MontoIng/AvRC-MA/Diseño (muestras)/Avión desvaliajo'.jpeg

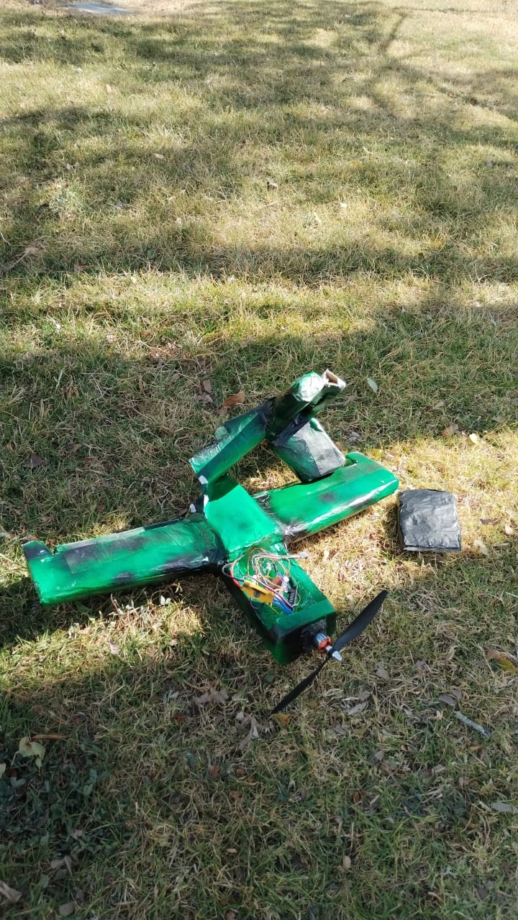
Diseño (muestras)/Avión desvaliajo'.jpeg
