MontoIng/AvRC-MA/Diseño (muestras)/Diseño avión.jpeg

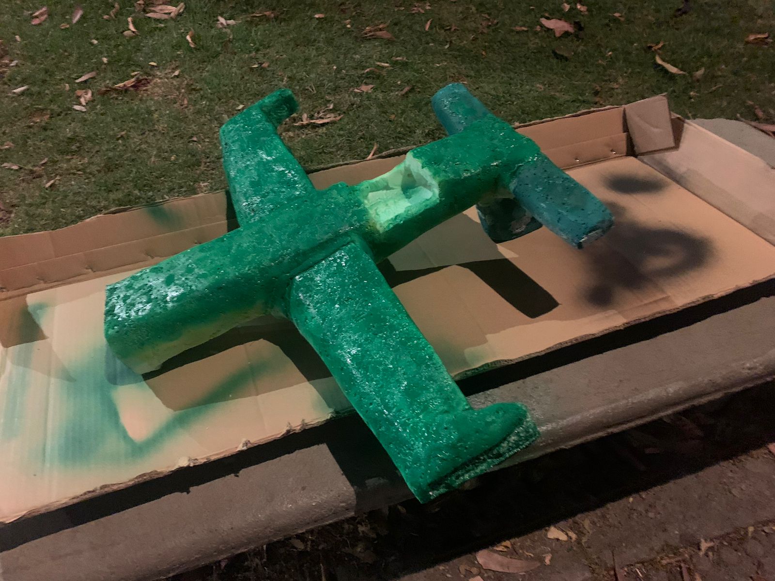
Diseño (muestras)/Diseño avión.jpeg
