MontoIng/AvRC-MA/Diseño (muestras)/Foto Avión - Control (en PROFI).jpeg

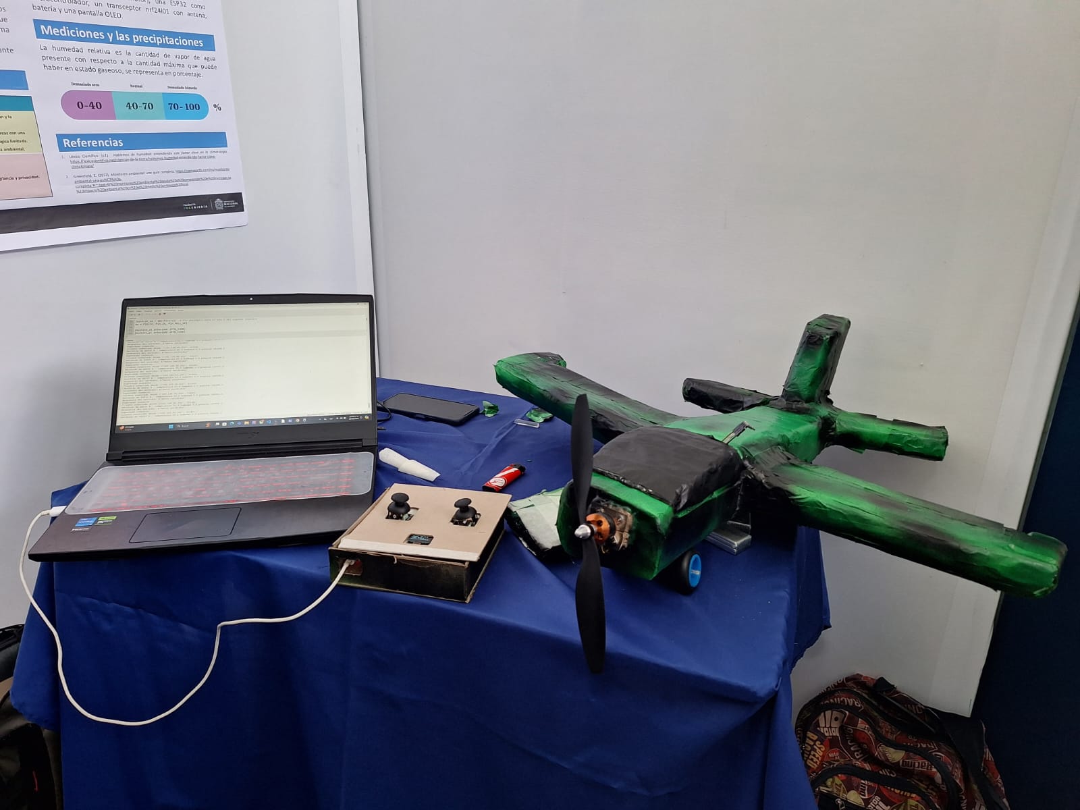
Diseño (muestras)/Foto Avión - Control (en PROFI).jpeg
