MontoIng/AvRC-MA/Documentos/Diagrama de Caja Negra.png

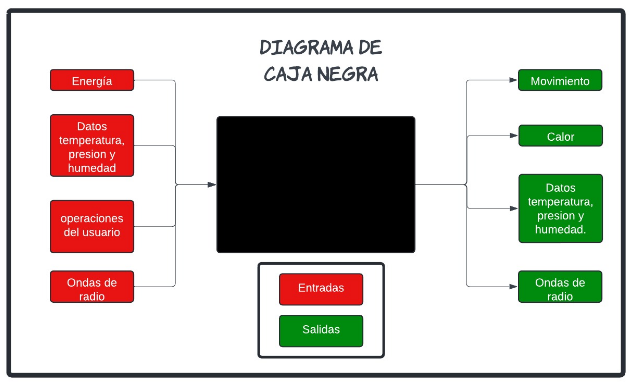
Documentos/Diagrama de Caja Negra.png
