MontoIng/AvRC-MA/Documentos/Diagrama Tecnológico.jpeg

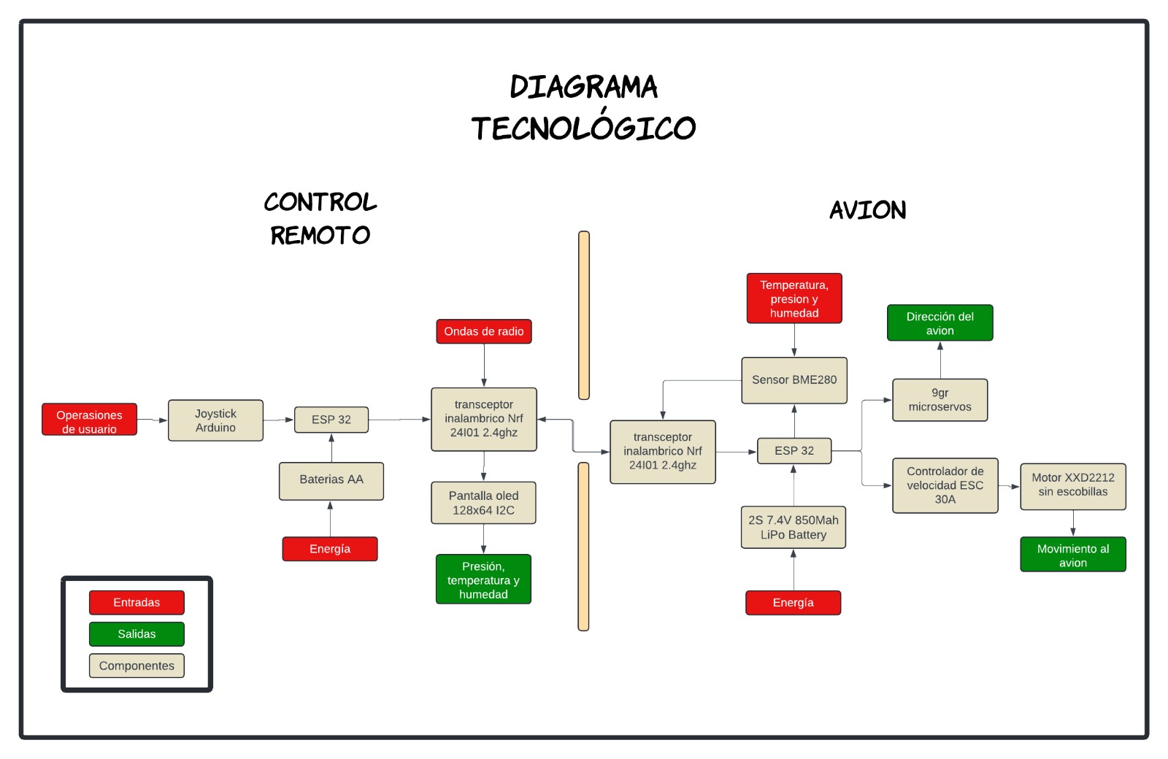
Documentos/Diagrama Tecnológico.jpeg
