MontoIng/AvRC-MA/Documentos/Función pantalla OLED (diagrama).jpeg

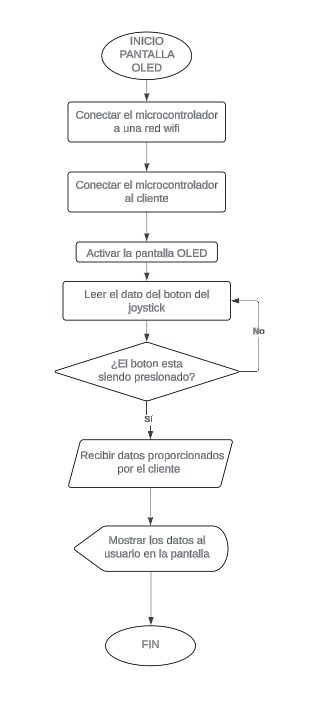
Documentos/Función pantalla OLED (diagrama).jpeg
