MontoIng/AvRC-MA/Documentos/Función sensor (diagrama).jpeg

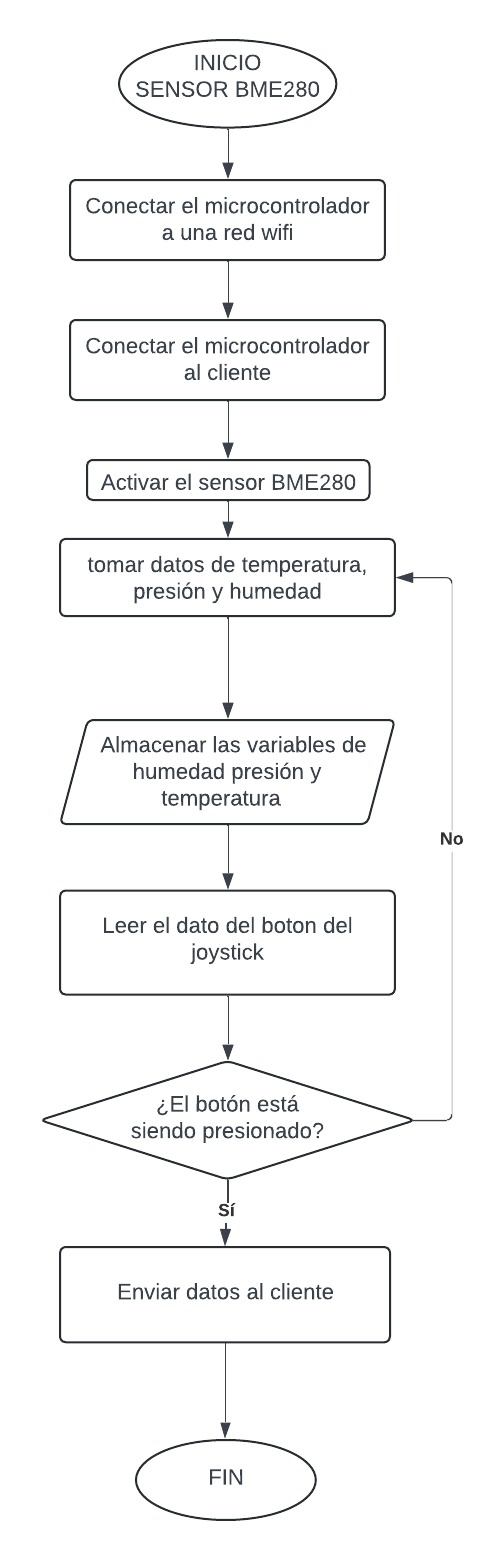
Documentos/Función sensor (diagrama).jpeg
