MontoIng/AvRC-MA/Documentos/Interacción desde motor (diagrama).jpeg

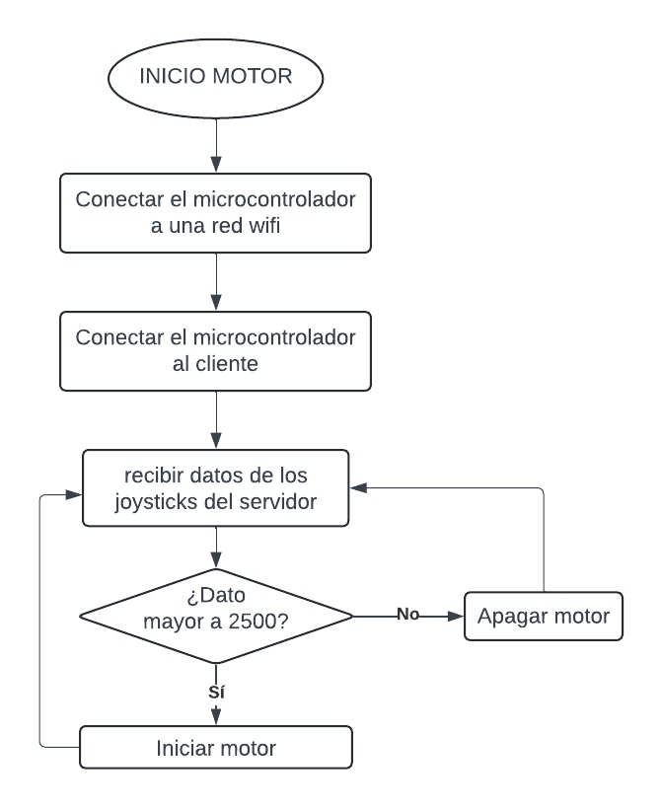
Documentos/Interacción desde motor (diagrama).jpeg
