MontoIng/AvRC-MA/Documentos/Interacción joysticks (diagrama).jpeg

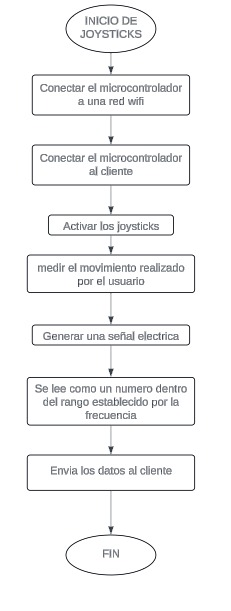
Documentos/Interacción joysticks (diagrama).jpeg
