MontoIng/AvRC-MA/Documentos/Programación del proyecto.png

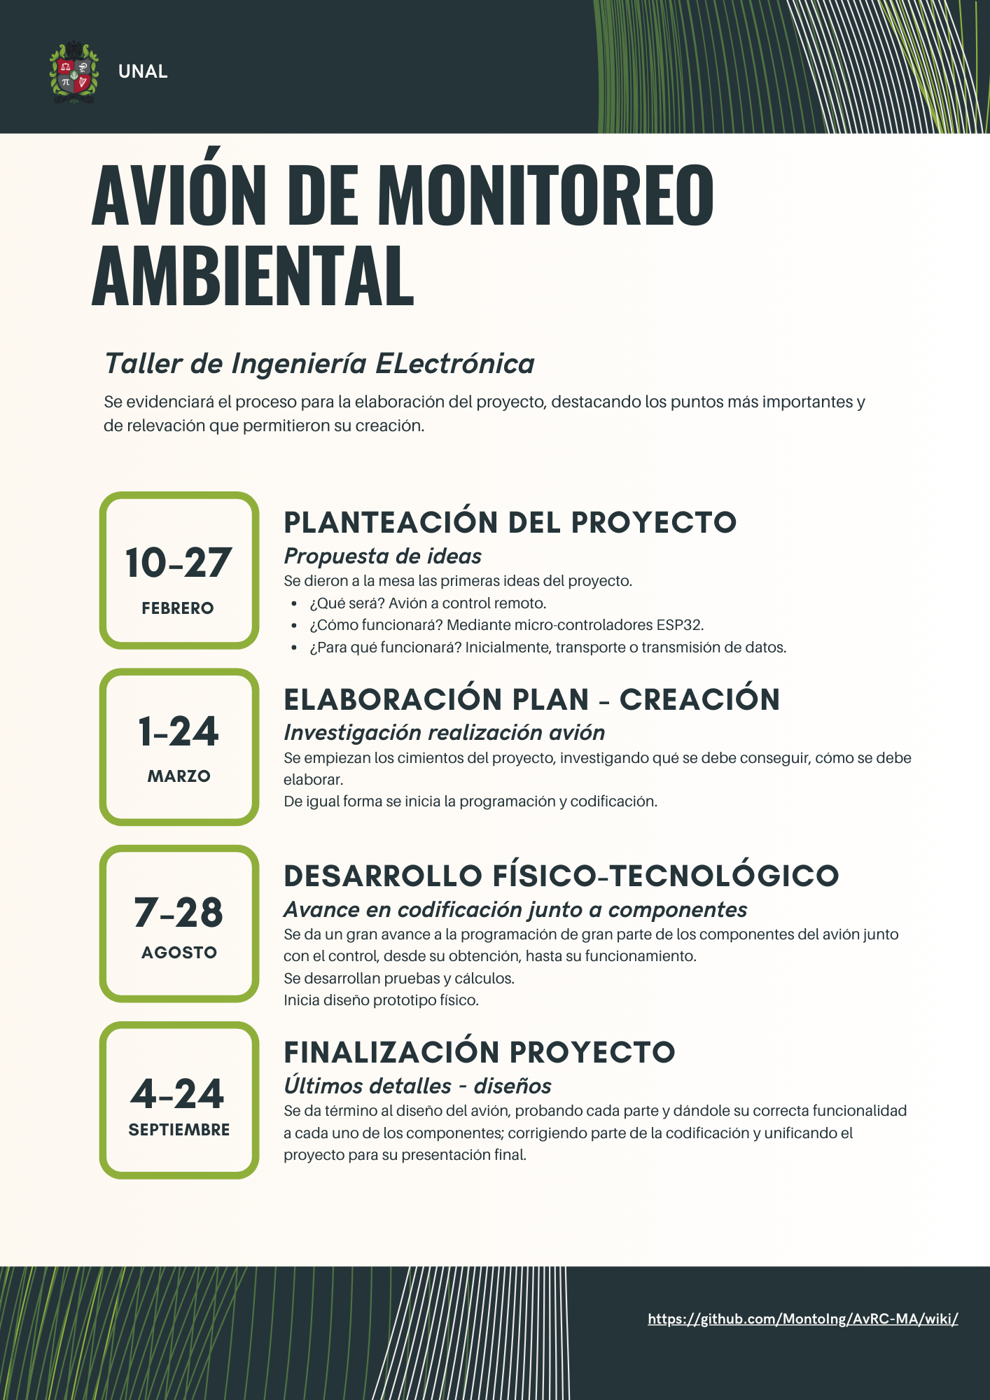
Documentos/Programación del proyecto.png
