MontoIng/AvRC-MA/PCBs/Imágenes (KiCad)/Avión/Diseño PCB Final (3D - Lado 1).png

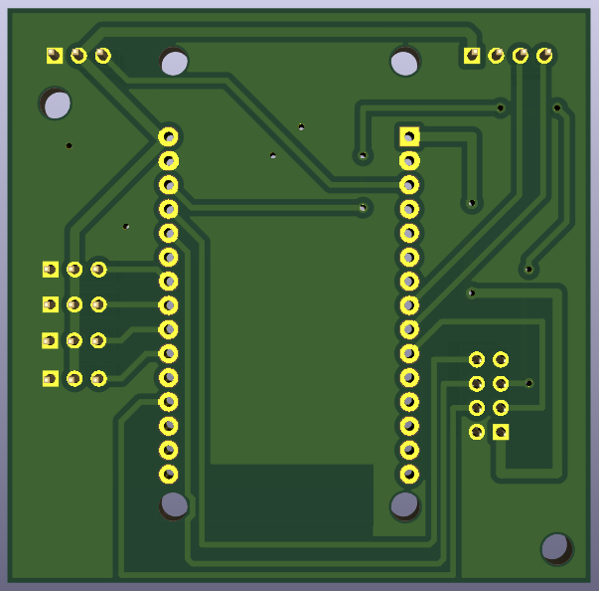
PCBs/Imágenes (KiCad)/Avión/Diseño PCB Final (3D - Lado 1).png
