MontoIng/AvRC-MA/PCBs/Imágenes (KiCad)/Avión/Diseño PCB Final (3D - Lado 2).png

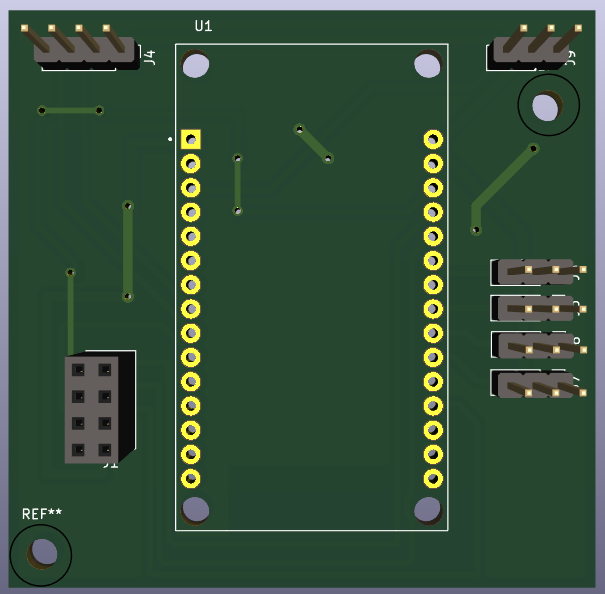
PCBs/Imágenes (KiCad)/Avión/Diseño PCB Final (3D - Lado 2).png
