MontoIng/AvRC-MA/PCBs/Imágenes (KiCad)/Control/Diseño de PCB layout (ruteo).png

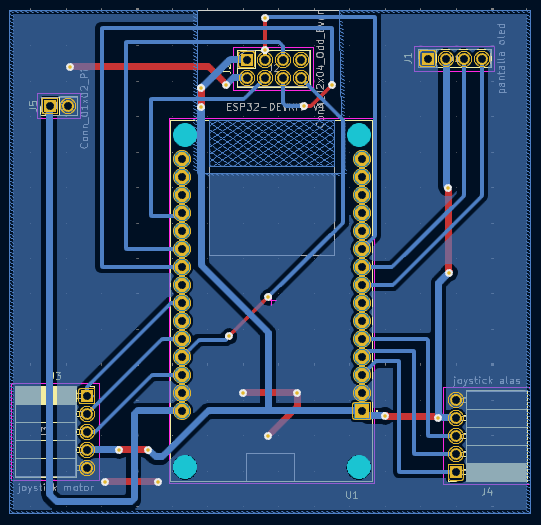
PCBs/Imágenes (KiCad)/Control/Diseño de PCB layout (ruteo).png
