MontoIng/AvRC-MA/PCBs/Imágenes (KiCad)/Control/Diseño PCB Final (3D - Lado 2).png

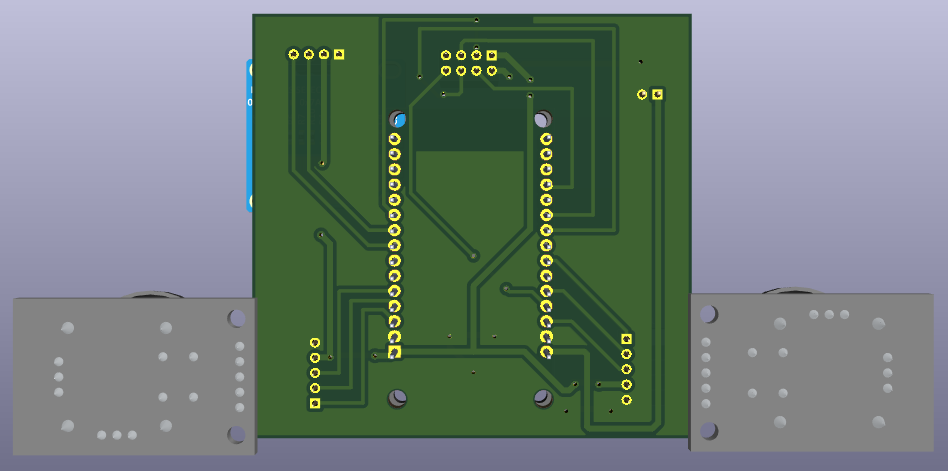
PCBs/Imágenes (KiCad)/Control/Diseño PCB Final (3D - Lado 2).png
