MontoIng/AvRC-MA/PCBs/PCB completa.jpeg

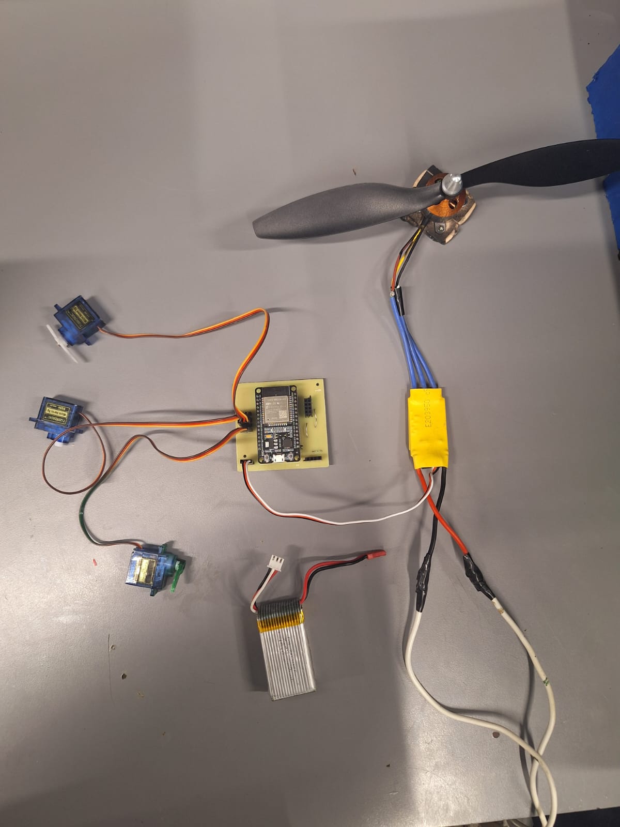
PCBs/PCB completa.jpeg
