MontoIng/AvRC-MA/PCBs/PCBs diseñadas.jpeg

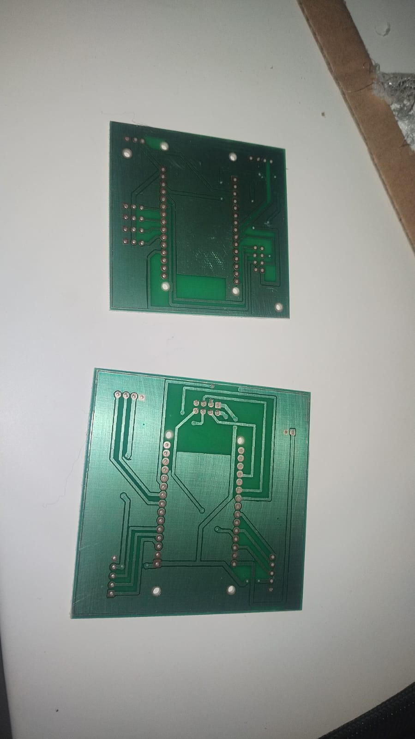
PCBs/PCBs diseñadas.jpeg
