MontoIng/AvRC-MA/PCBs/PCB (componentes soldados).jpeg

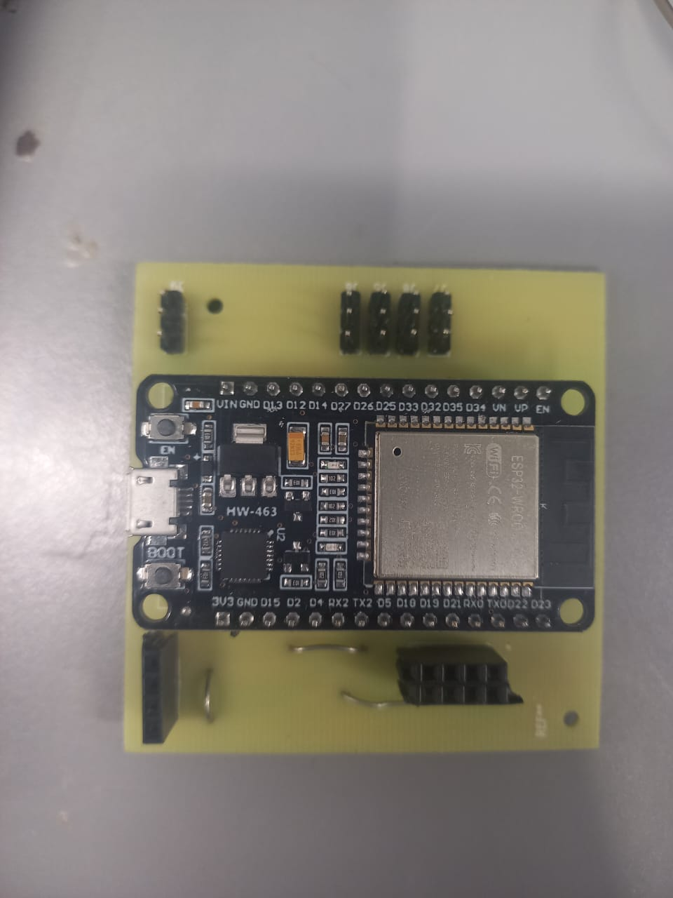
PCBs/PCB (componentes soldados).jpeg
