MontoIng/AvRC-MA/PCBs/PCB Fabricada.jpeg

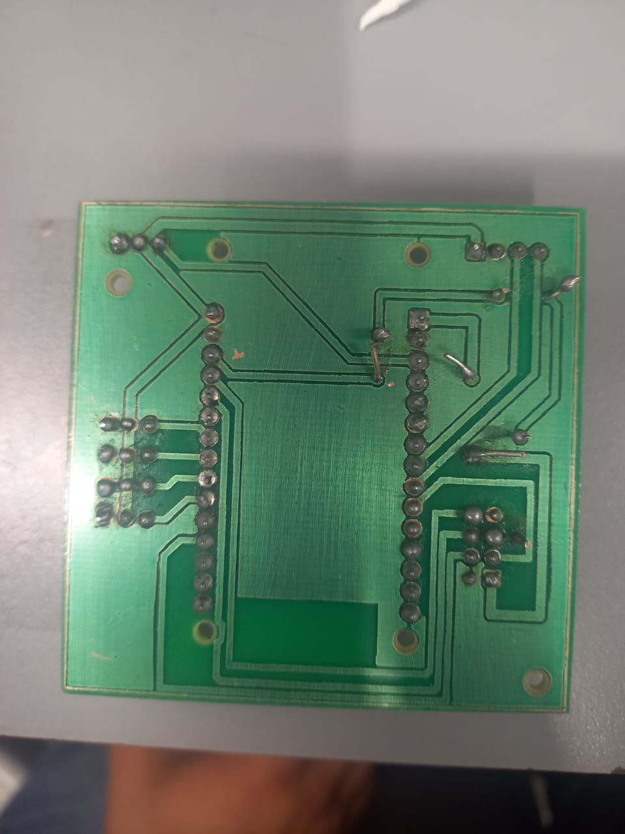
PCBs/PCB Fabricada.jpeg
